MiggeJ71/Firebeetle_BME280/Firebeetle_BME280_schema.kicad_sch

## KiCad design Firebeetle_BME280_schema.kicad_sch (2022-01-31)

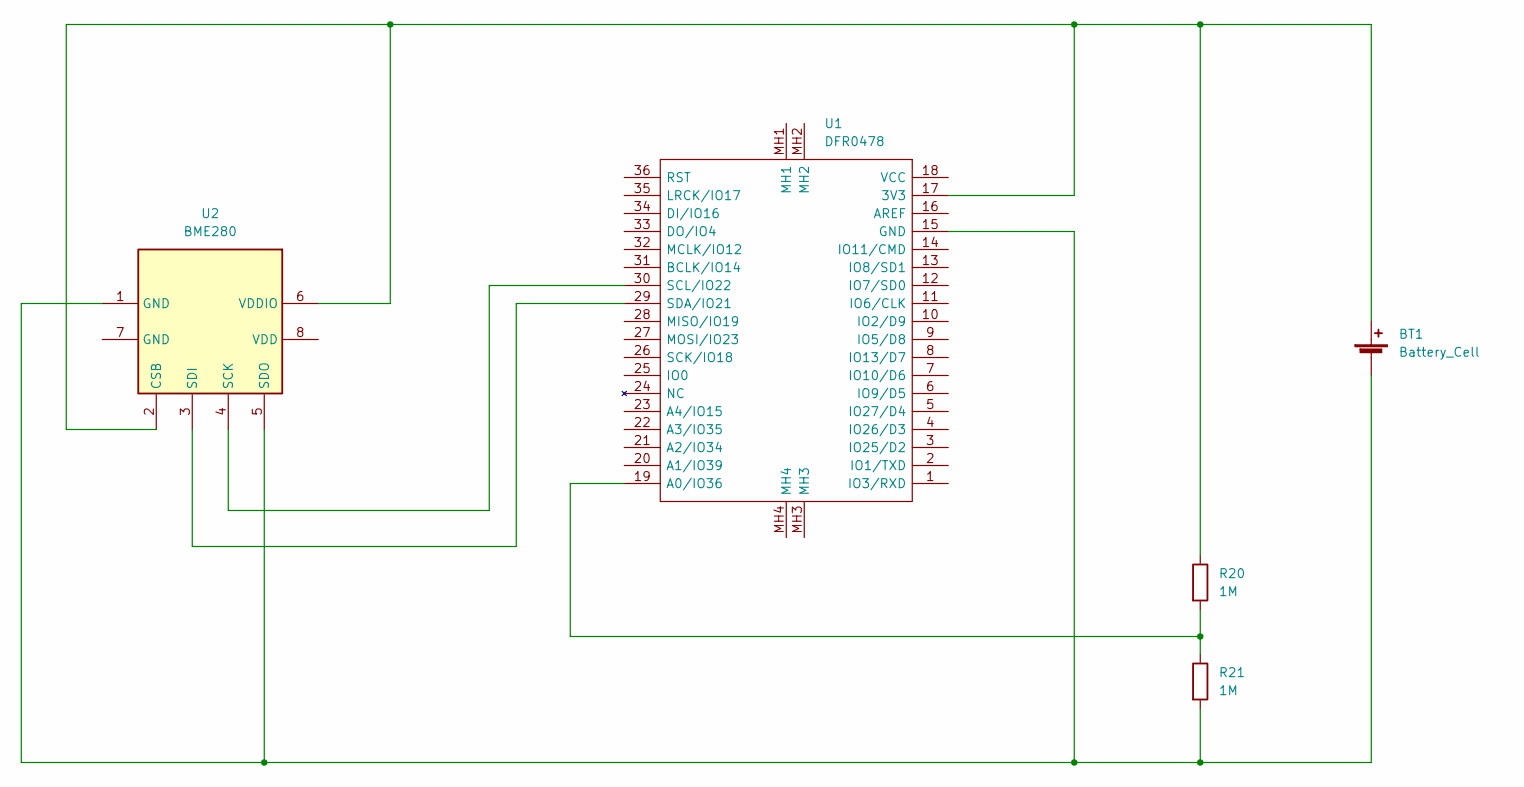
[picture p3: schematic Firebeetle_BME280_schema.kicad_sch]

Parts:
BT1: Battery_Cell
R20, R21: 1M
U1: DFR0478; FIREBEETLE_ESP32; Manufacturer_Part_Number DFR0478; Mouser Part Number 426-DFR0478
U2: BME280; Bosch_LGA-8_2.5x2.5mm_P0.65mm_ClockwisePinNumbering

Connections:
unnamed: BT1.1 (+), R20.1, U1.17 (3V3), U2.2 (CSB), U2.6 (VDDIO)
unnamed: BT1.2 (-), R21.2, U1.15 (GND), U2.1 (GND), U2.5 (SDO)
unnamed: R20.2, R21.1, U1.19 (A0/IO36)
unnamed: U1.29 (SDA/IO21), U2.3 (SDI)
unnamed: U1.30 (SCL/IO22), U2.4 (SCK)
